Moonspine/faux-analog-clock/Firmware/Faux_Analog_Clock/SevenSegment.h

#ifndef SEVEN_SEGMENT_H
#define SEVEN_SEGMENT_H

#include "Arduino.h"
#include "FrameBufferView.h"

const PROGMEM uint8_t SEVEN_SEGMENT_ASCII_TABLE[] = {
  0b00000000, 0b00000000, 0b00000000, 0b00000000, 0b00000000, 0b00000000, 0b00000000, 0b00000000, // 0x00..0x07
  0b00000000, 0b00000000, 0b00000000, 0b00000000, 0b00000000, 0b00000000, 0b00000000, 0b00000000, // 0x08..0x0f
  0b00000000, 0b00000000, 0b00000000, 0b00000000, 0b00000000, 0b00000000, 0b00000000, 0b00000000, // 0x10..0x17
  0b00000000, 0b00000000, 0b00000000, 0b00000000, 0b00000000, 0b00000000, 0b00000000, 0b00000000, // 0x18..0x1f
  0b00000000, 0b00110000, 0b00100010, 0b01111110, 0b00101101, 0b01010010, 0b01111011, 0b00000010, // 0x20..0x27
  0b00111001, 0b00001111, 0b01100011, 0b01000110, 0b00010000, 0b01000000, 0b00010000, 0b01010010, // 0x28..0x2f
  0b00111111, 0b00000110, 0b01011011, 0b01001111, 0b01100110, 0b01101101, 0b01111100, 0b00000111, // 0x30..0x37
  0b01111111, 0b01100111, 0b00001001, 0b00000101, 0b01011000, 0b01001000, 0b01001100, 0b01010011, // 0x38..0x3f
  0b01011100, 0b01110111, 0b01111100, 0b00111001, 0b01011110, 0b01111001, 0b01110001, 0b00111101, // 0x40..0x47
  0b01110110, 0b00110000, 0b00011110, 0b01110100, 0b00111000, 0b00110111, 0b01010100, 0b00111111, // 0x48..0x4f
  0b01110011, 0b01100111, 0b01010000, 0b01101101, 0b00000111, 0b00111110, 0b00111110, 0b00111110, // 0x50..0x57
  0b01110110, 0b01100110, 0b01011011, 0b00111001, 0b01100100, 0b00001111, 0b00100011, 0b00001000, // 0x58..0x5f
  0b00100000, 0b01110111, 0b01111100, 0b01011000, 0b01011110, 0b01111001, 0b01110001, 0b01101111, // 0x60..0x67
  0b01110100, 0b00010000, 0b00011110, 0b01110100, 0b00110000, 0b00110111, 0b01010100, 0b01011100, // 0x68..0x6f
  0b01110011, 0b01100111, 0b01010000, 0b01101101, 0b01000100, 0b00011100, 0b00011100, 0b00111110, // 0x70..0x77
  0b01110110, 0b01100110, 0b01011011, 0b00111001, 0b00000110, 0b00001111, 0b01000000, 0b00000000  // 0x78..0x7f
};

/*
 *       A
 *     F   B
 *       G
 *     E   C
 *       D
 */

// 0GFEDCBA

/**
 * Writes the given ASCII character to the given 7-segment display buffer
 * 
 * @param frameBuffer The buffer to write to
 * @param value The character to write
 * @param brightness The display brightness of the character
 */
void writeSevenSegmentDisplay(FrameBufferView *frameBuffer, char value, uint8_t brightness);

#endif
